Harwasch/CuttleProgrammerJig/cad/out/p100/v_exploded.png

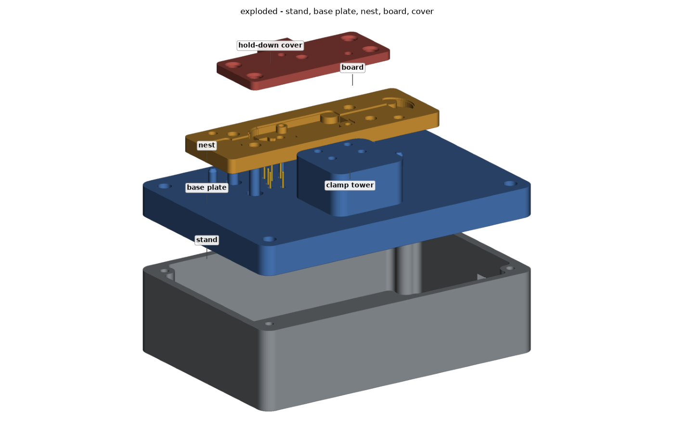
cad/out/p100/v_exploded.png
