Harwasch/CuttleProgrammerJig/cad/out/p100/v_front.png

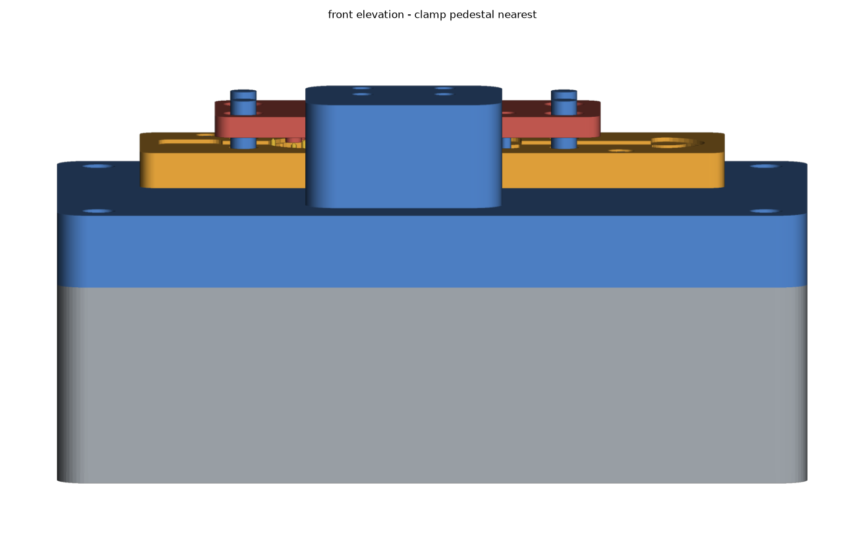
cad/out/p100/v_front.png
