Harwasch/CuttleProgrammerJig/cad/out/p100/v_gauge.png

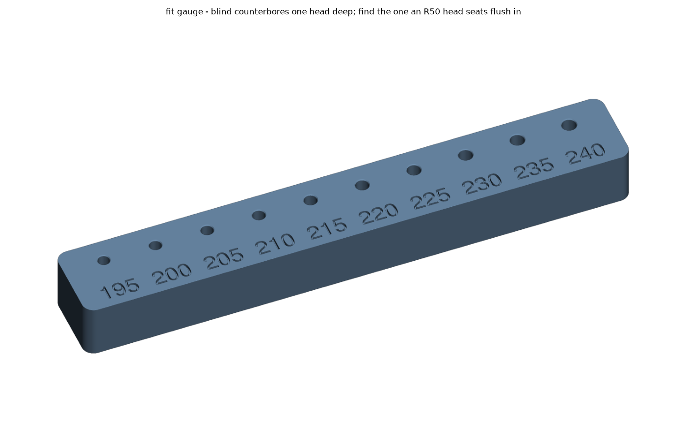
cad/out/p100/v_gauge.png
