Harwasch/CuttleProgrammerJig/cad/out/p100/v_iso_front_left.png

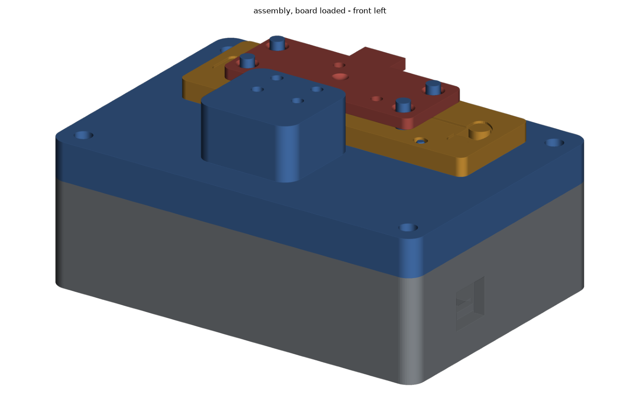
cad/out/p100/v_iso_front_left.png
