Harwasch/CuttleProgrammerJig/cad/out/p100/v_iso_front_right.png

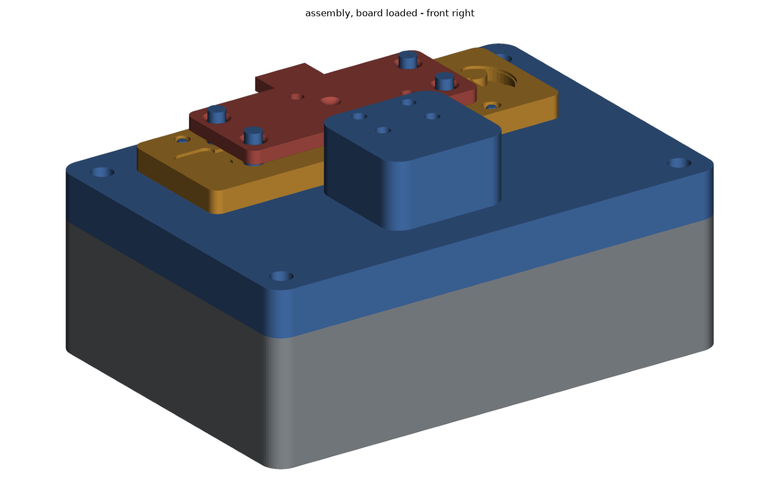
cad/out/p100/v_iso_front_right.png
