Harwasch/CuttleProgrammerJig/cad/out/p100/v_iso_high.png

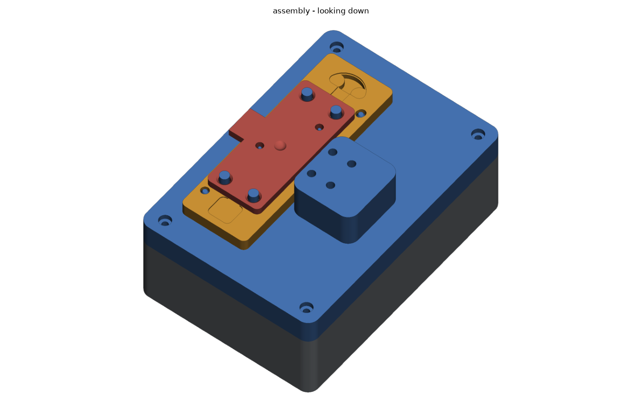
cad/out/p100/v_iso_high.png
