Harwasch/CuttleProgrammerJig/cad/out/p100/v_iso_rear.png

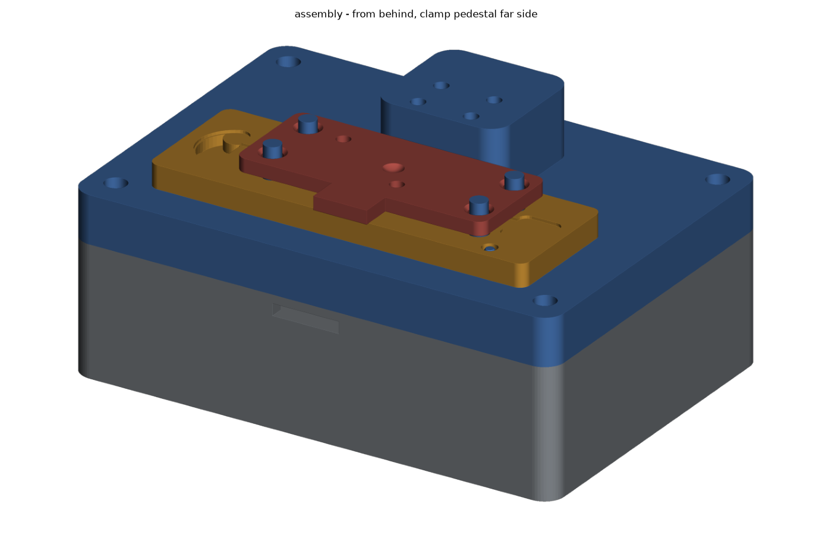
cad/out/p100/v_iso_rear.png
