Harwasch/CuttleProgrammerJig/cad/out/p100/v_jig_only.png

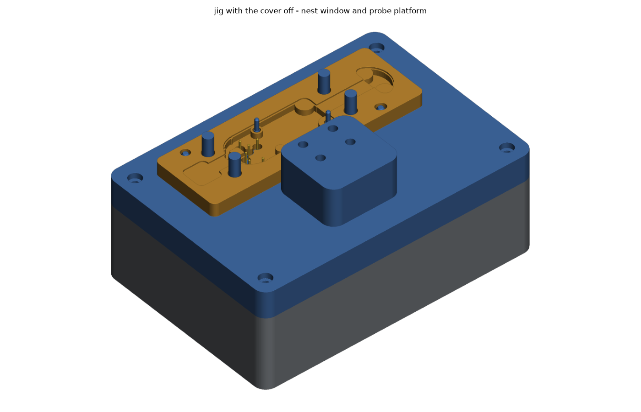
cad/out/p100/v_jig_only.png
