Harwasch/CuttleProgrammerJig/cad/out/p100/v_nest_probes.png

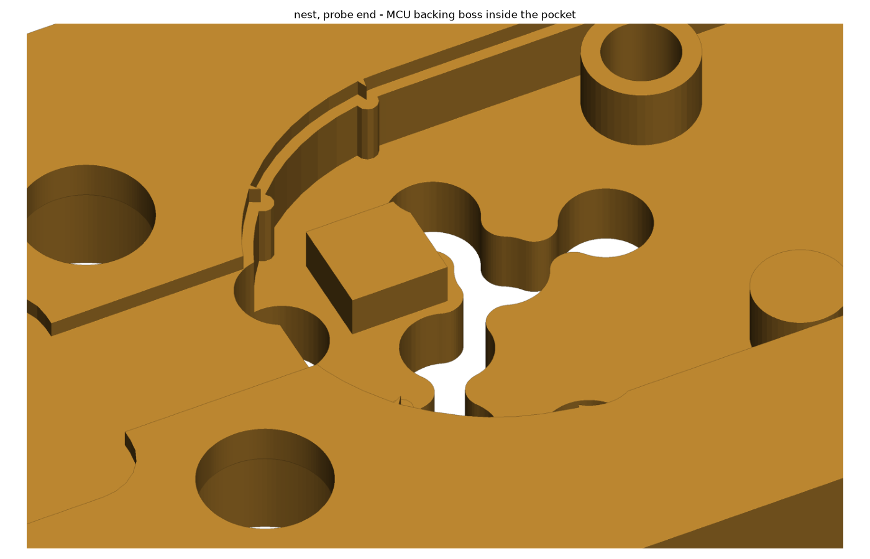
cad/out/p100/v_nest_probes.png
