Harwasch/CuttleProgrammerJig/cad/out/p100/v_open.png

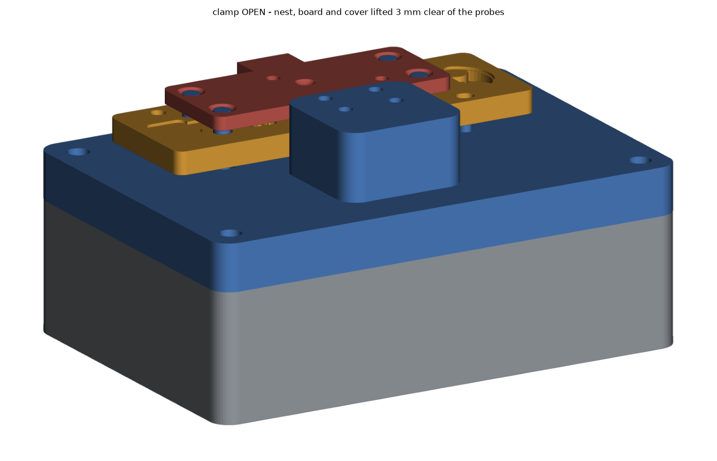
cad/out/p100/v_open.png
