Harwasch/CuttleProgrammerJig/cad/out/p100/v_probes.png

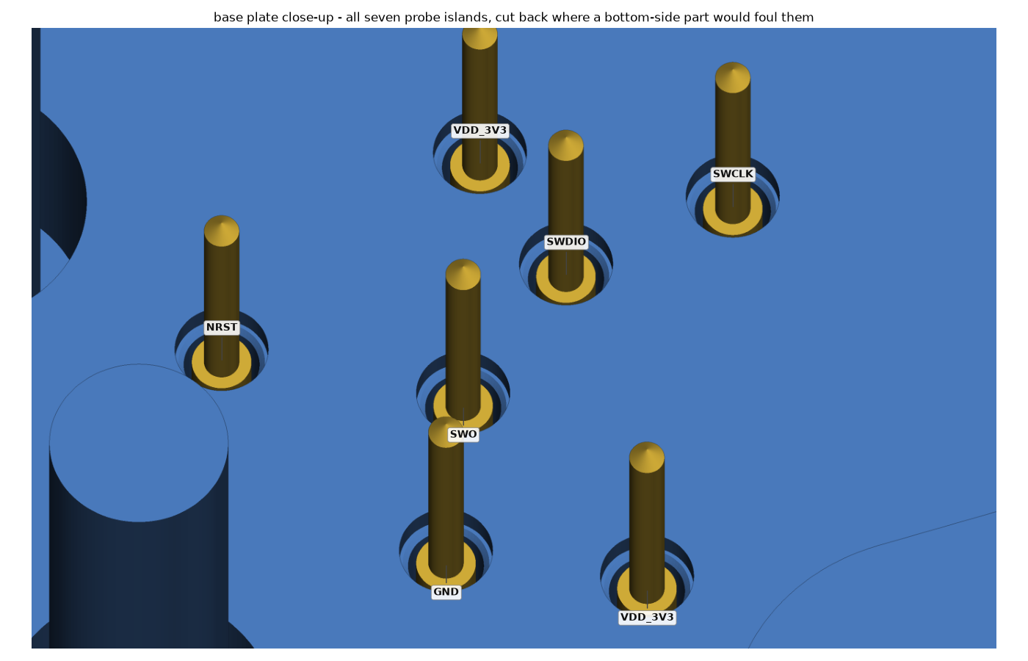
cad/out/p100/v_probes.png
