Harwasch/CuttleProgrammerJig/cad/out/p100/v_probes_board.png

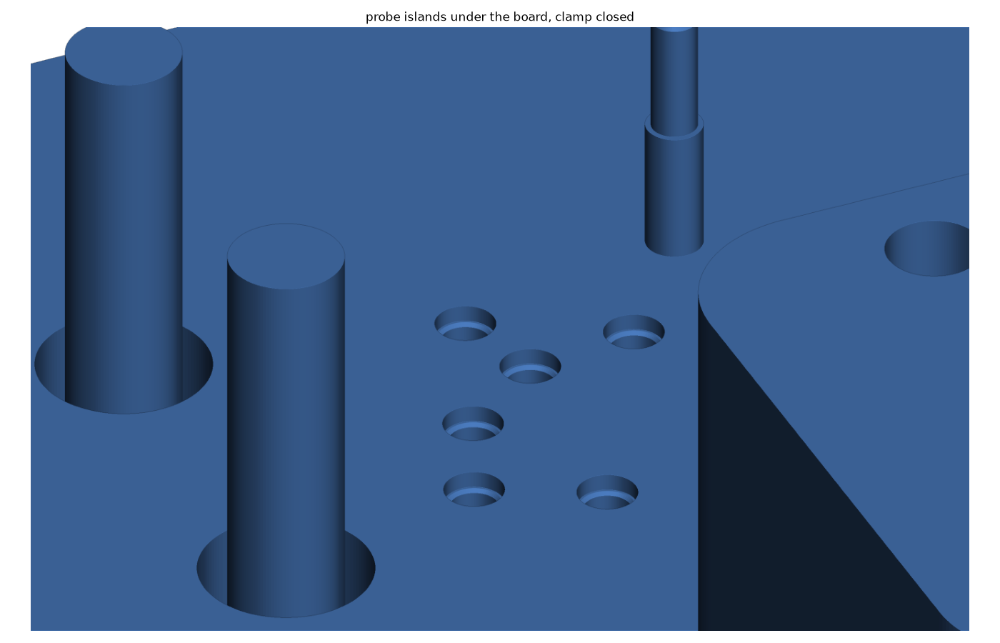
cad/out/p100/v_probes_board.png
