Harwasch/CuttleProgrammerJig/cad/out/p100/v_underside.png

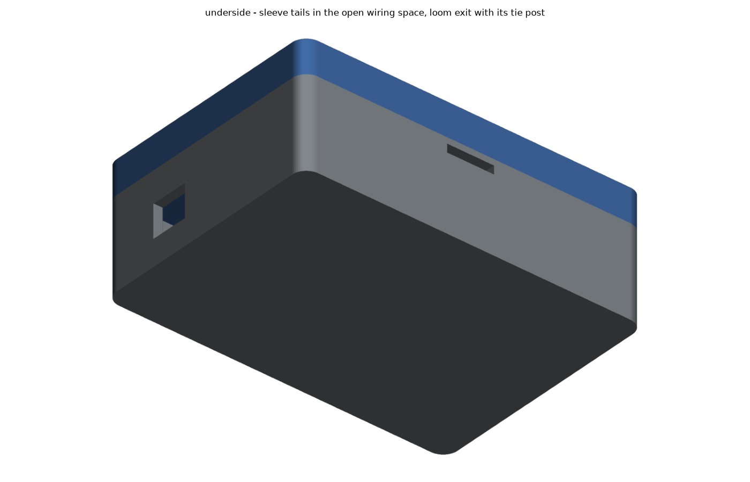
cad/out/p100/v_underside.png
