Harwasch/CuttleProgrammerJig/cad/out/v_flares.png

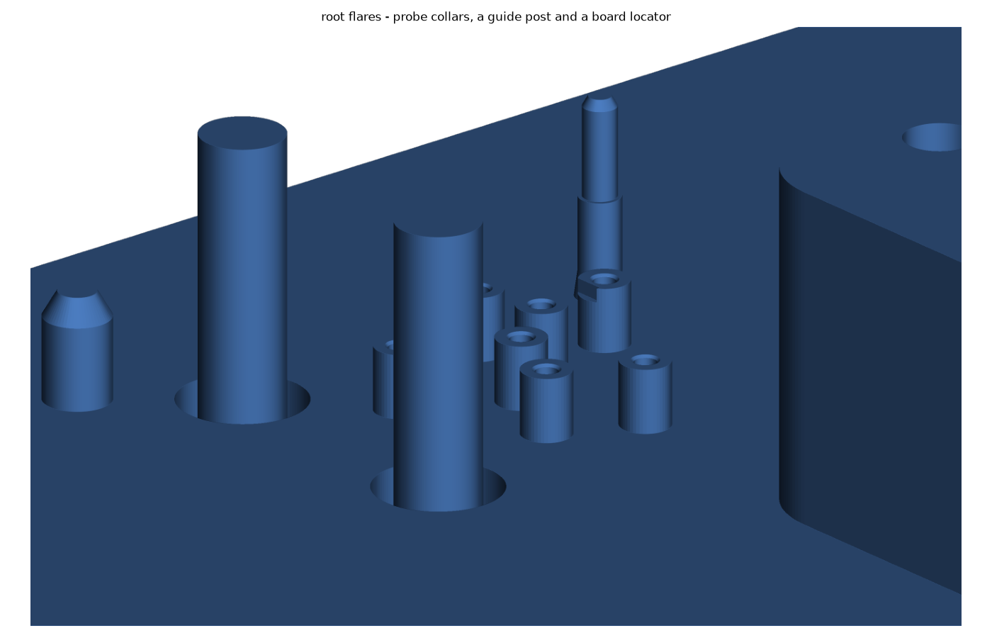
cad/out/v_flares.png
