Harwasch/CuttleProgrammerJig/cad/out/v_front.png

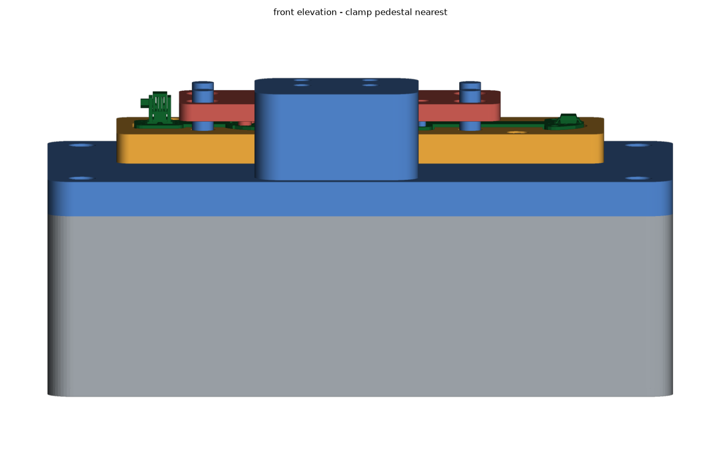
cad/out/v_front.png
