Harwasch/CuttleProgrammerJig/cad/out/v_iso_front_left.png

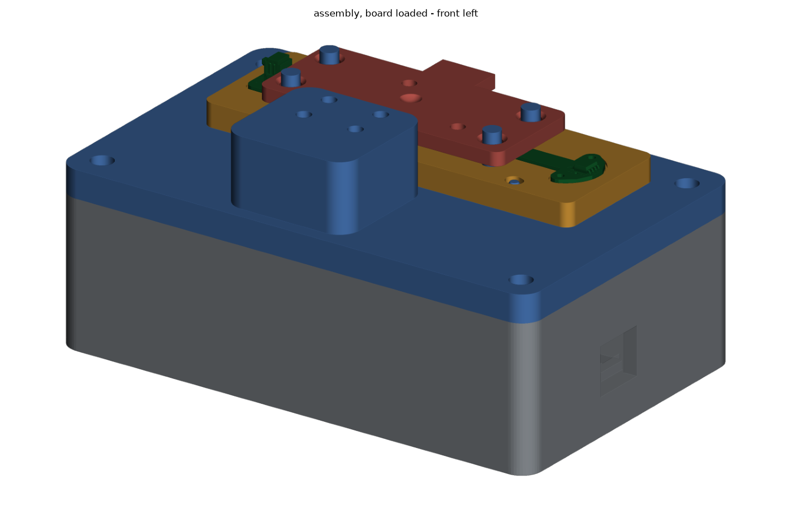
cad/out/v_iso_front_left.png
