Harwasch/CuttleProgrammerJig/cad/out/v_iso_rear.png

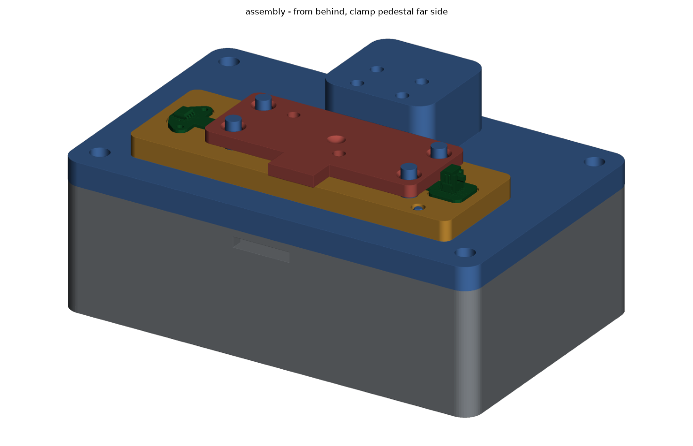
cad/out/v_iso_rear.png
