Harwasch/CuttleProgrammerJig/cad/out/v_probes_board.png

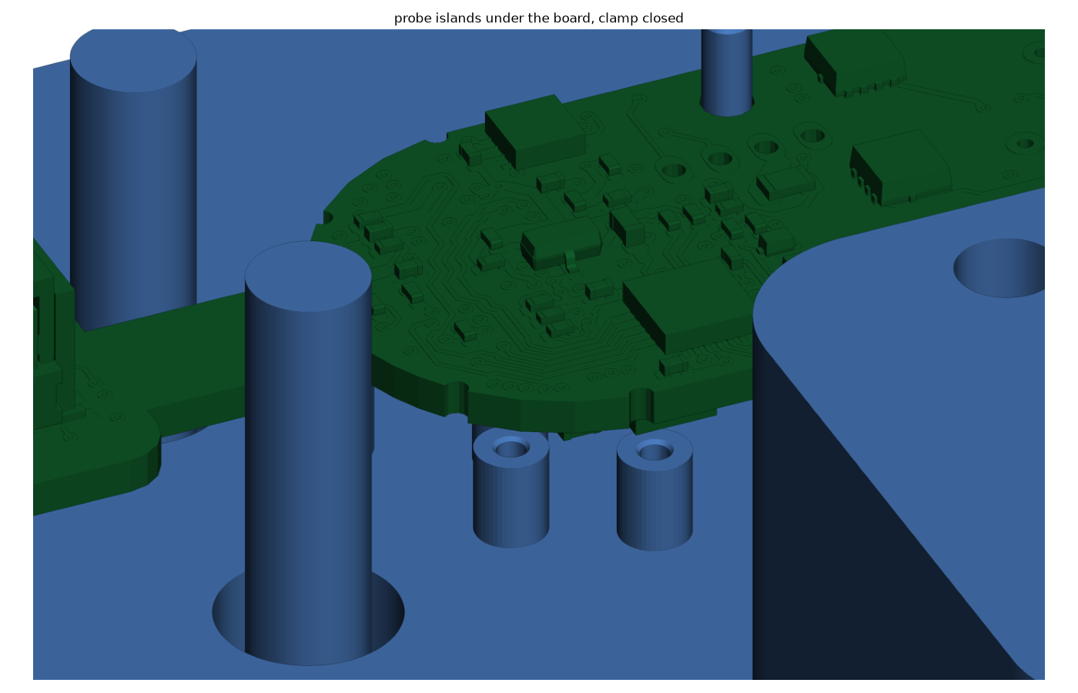
cad/out/v_probes_board.png
