Harwasch/CuttleProgrammerJig/cad/out/v_seat.png

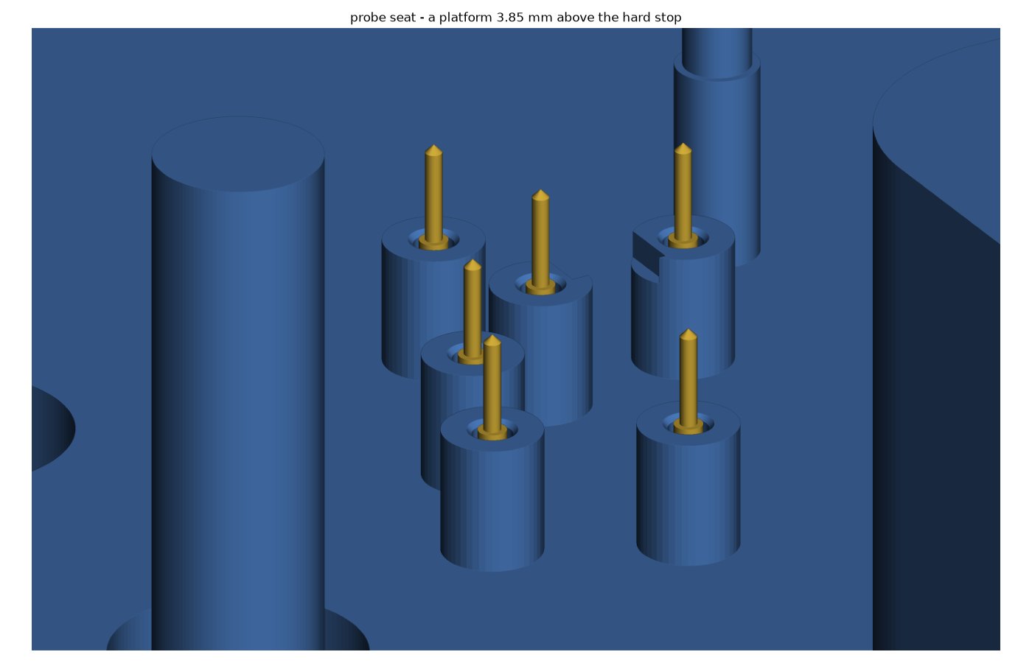
cad/out/v_seat.png
