Harwasch/CuttleProgrammerJig/cad/out/v_shrink_gauge.png

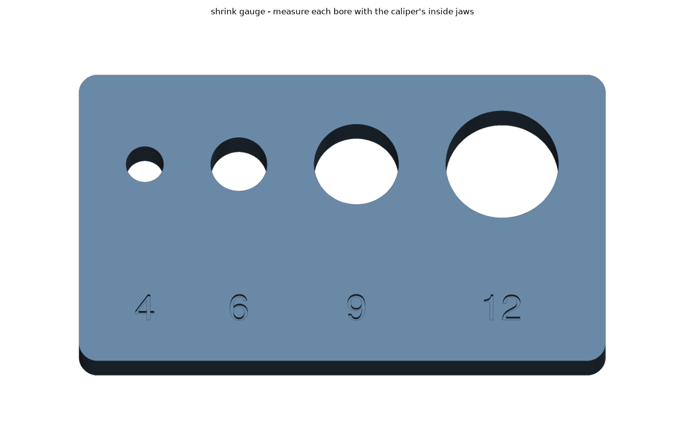
cad/out/v_shrink_gauge.png
