Harwasch/CuttleProgrammerJig/cad/out/v_side.png

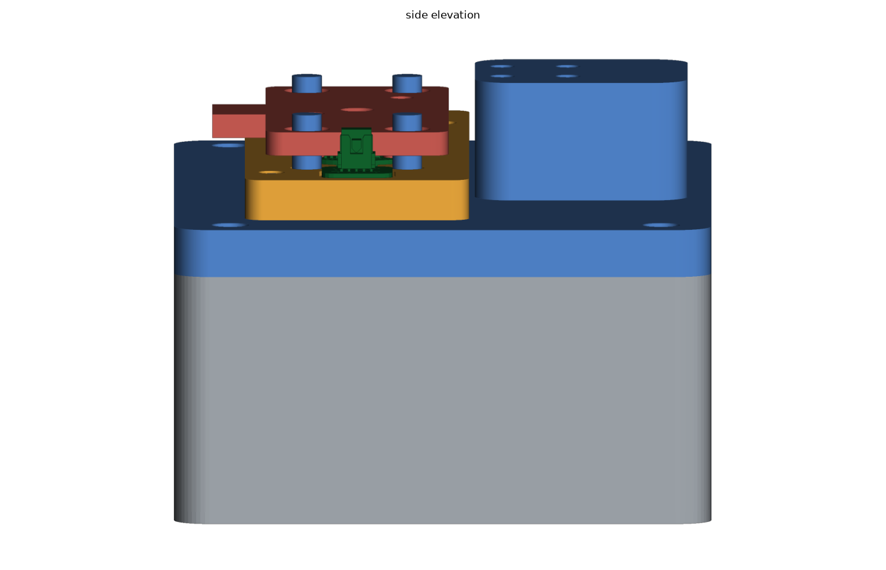
cad/out/v_side.png
