Harwasch/CuttleProgrammerJig/cad/out/v_stand_top.png

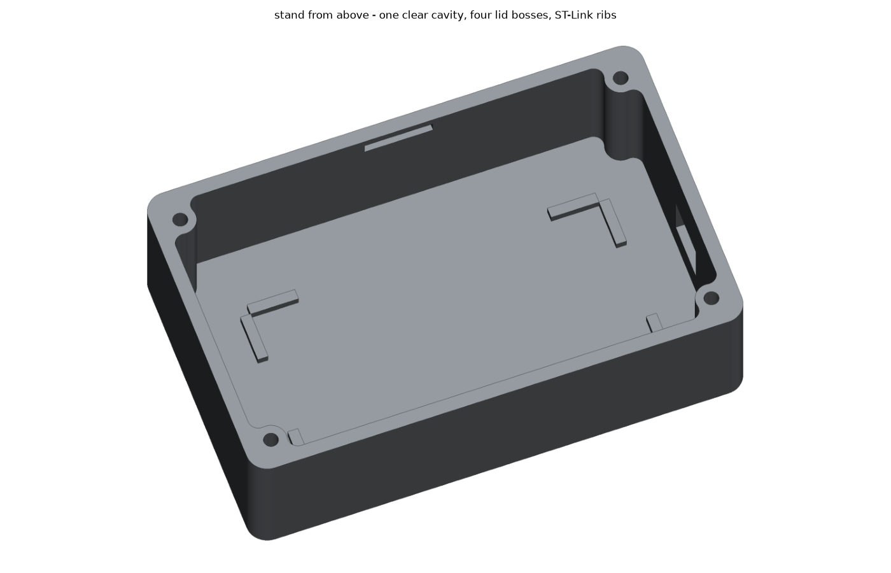
cad/out/v_stand_top.png
