Harwasch/CuttleProgrammerJig/magfixture/out/v_body.png

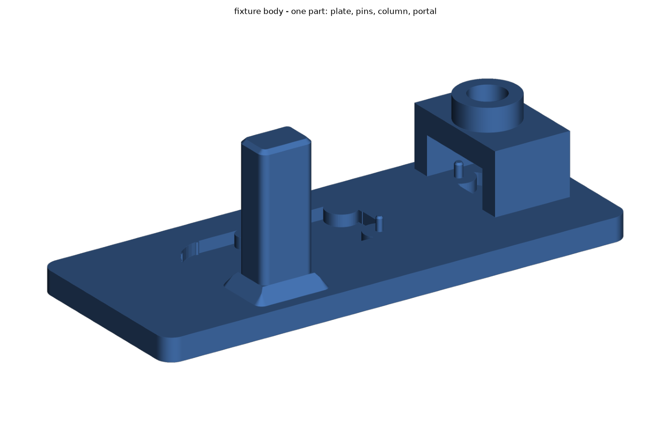
magfixture/out/v_body.png
