Harwasch/CuttleProgrammerJig/magfixture/out/v_encoder.png

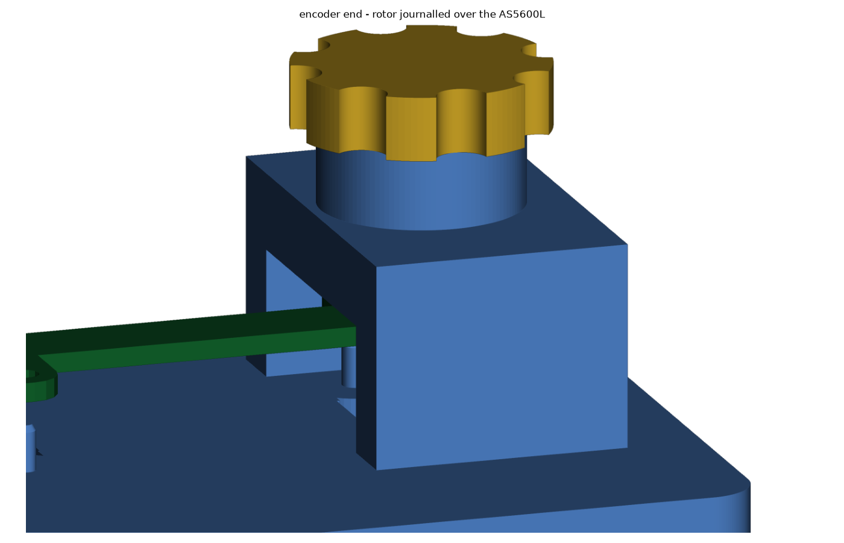
magfixture/out/v_encoder.png
