Harwasch/CuttleProgrammerJig/magfixture/out/v_hall.png

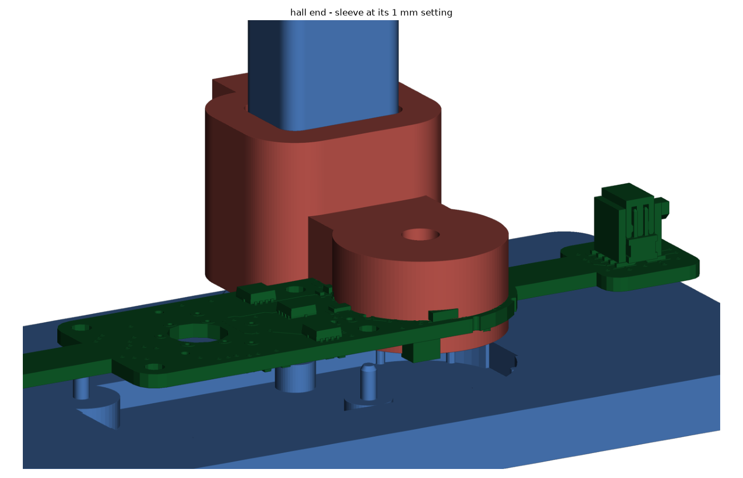
magfixture/out/v_hall.png
