Harwasch/CuttleProgrammerJig/magfixture/out/v_sleeve.png

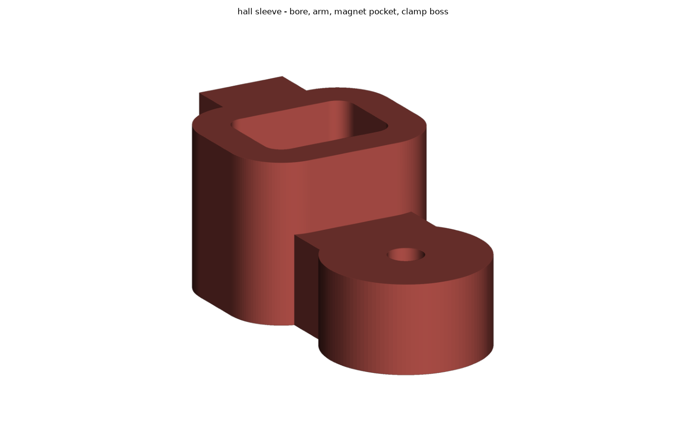
magfixture/out/v_sleeve.png
