Harwasch/CuttleProgrammerJig/magfixture/out/v_parts.png

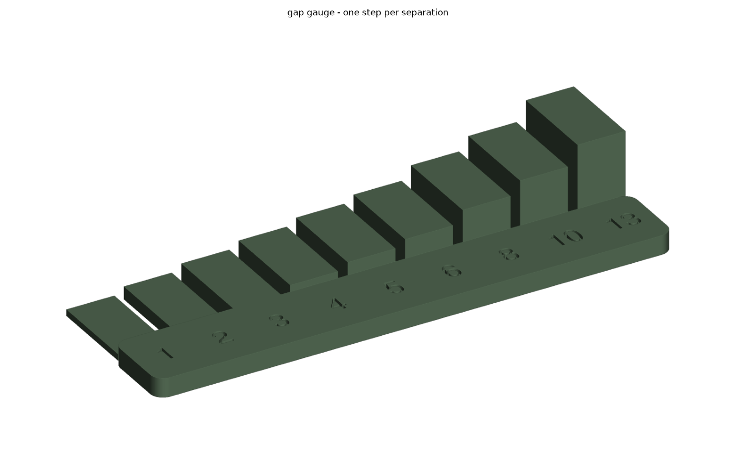
magfixture/out/v_parts.png
