Harwasch/CuttleProgrammerJig/magfixture/out/fixture_body.step

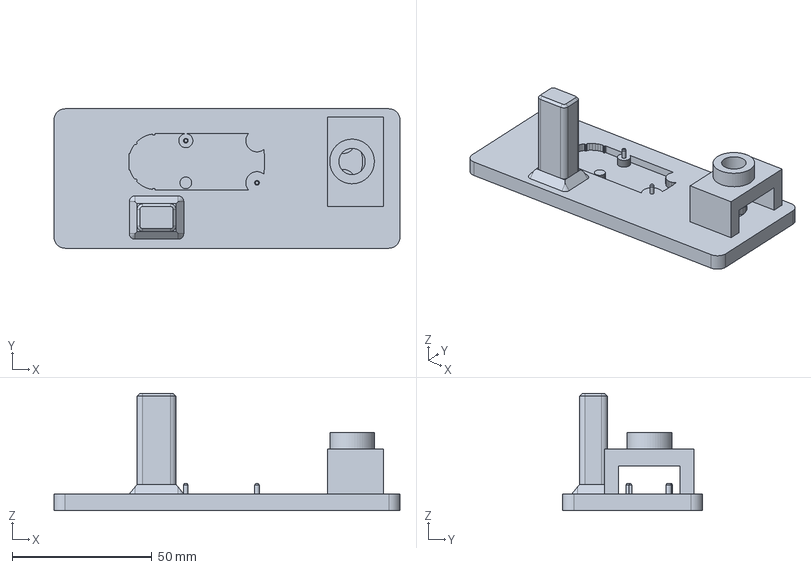
[picture p58: CAD file, 2026-09-14]
magfixture/out/fixture_body.step
124.0 x 50.0 x 42.0 mm
