Harwasch/CuttleProgrammerJig/cad/out/p100/v_wiring.png

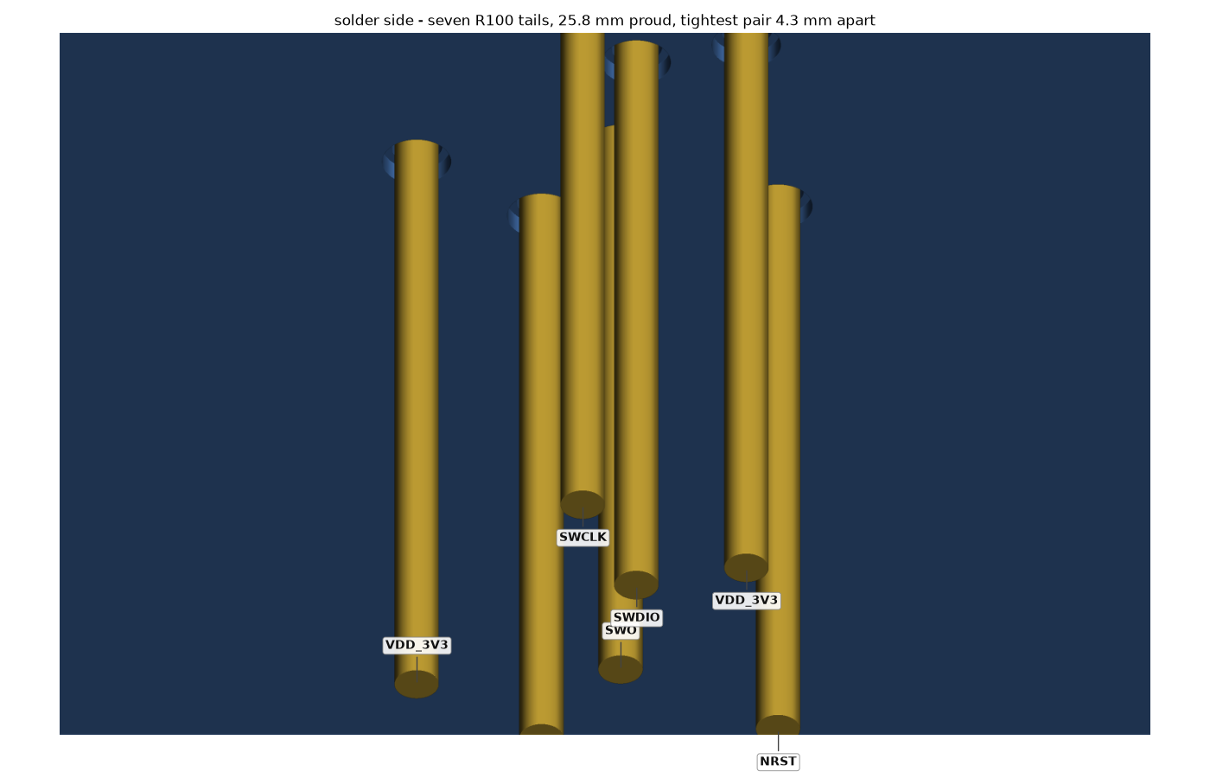
cad/out/p100/v_wiring.png
