Harwasch/CuttleProgrammerJig/magfixture/out/v_assembled.png

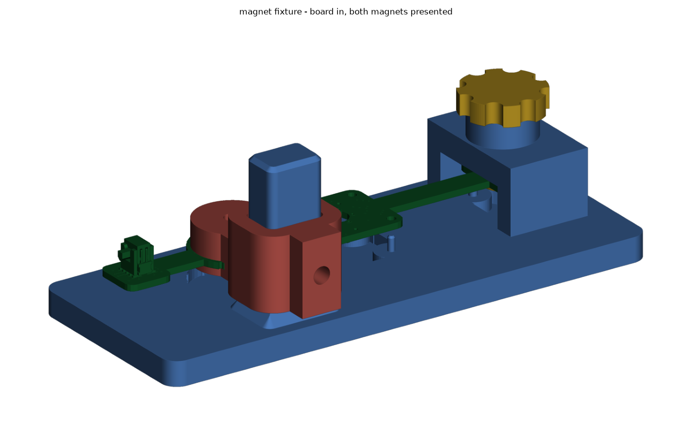
magfixture/out/v_assembled.png
